richelbilderbeek/MinimalPiClock/docs/casing/sphere_cut.png

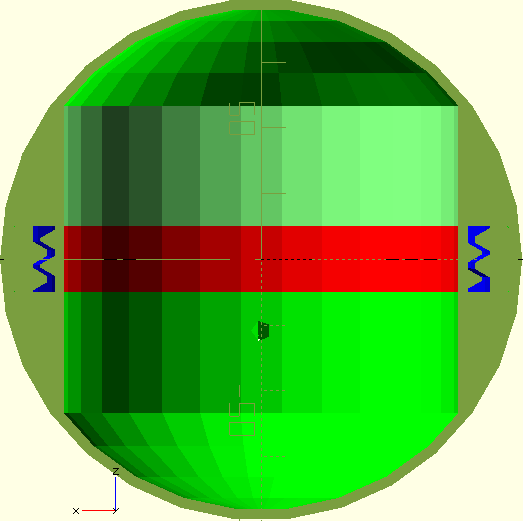
docs/casing/sphere_cut.png
