richelbilderbeek/MinimalPiClock/docs/casing/sphere_cut_annotated.png

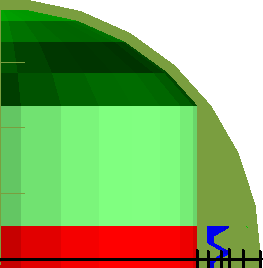
docs/casing/sphere_cut_annotated.png
