richelbilderbeek/MinimalPiClock/docs/photos/20260625_casing_1.jpg

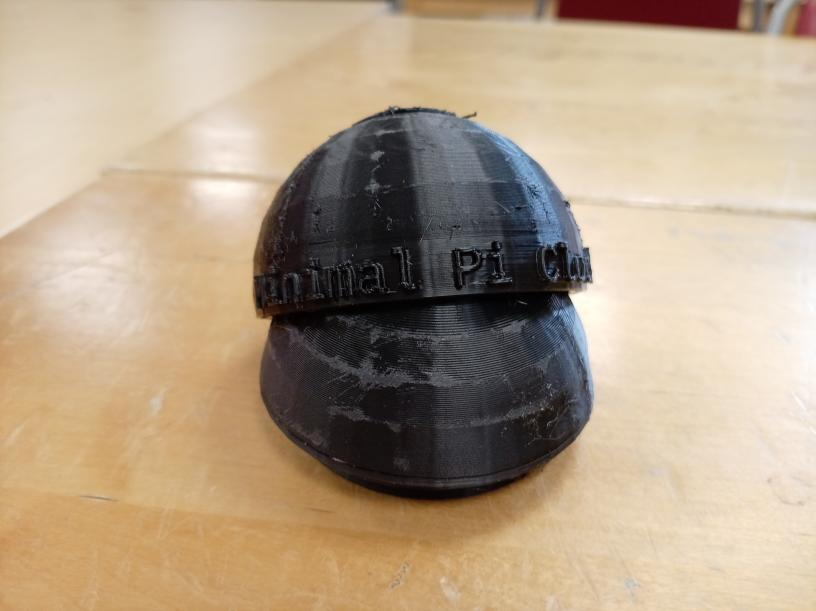
docs/photos/20260625_casing_1.jpg
