richelbilderbeek/MinimalPiClock/docs/photos/20260625_casing_2.jpg

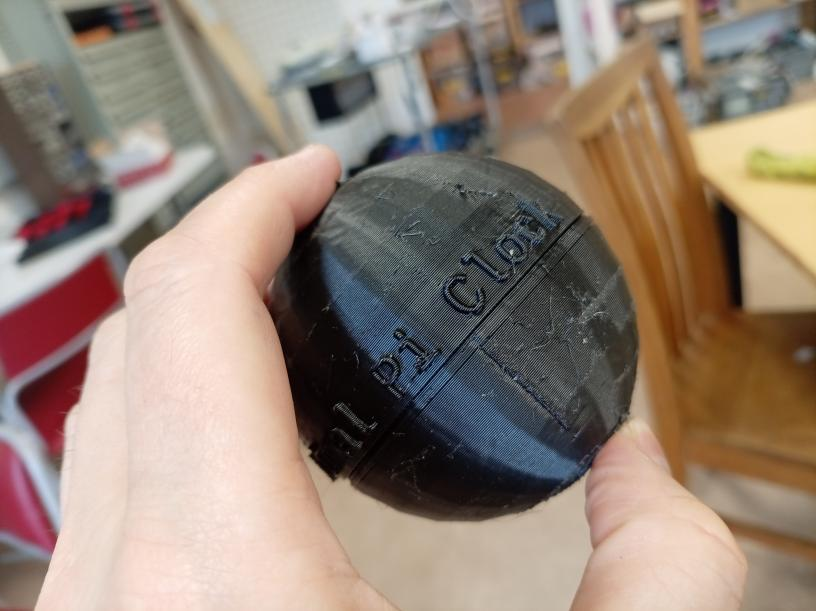
docs/photos/20260625_casing_2.jpg
